linuskjk/CableProbe/zine/cool-bg.png

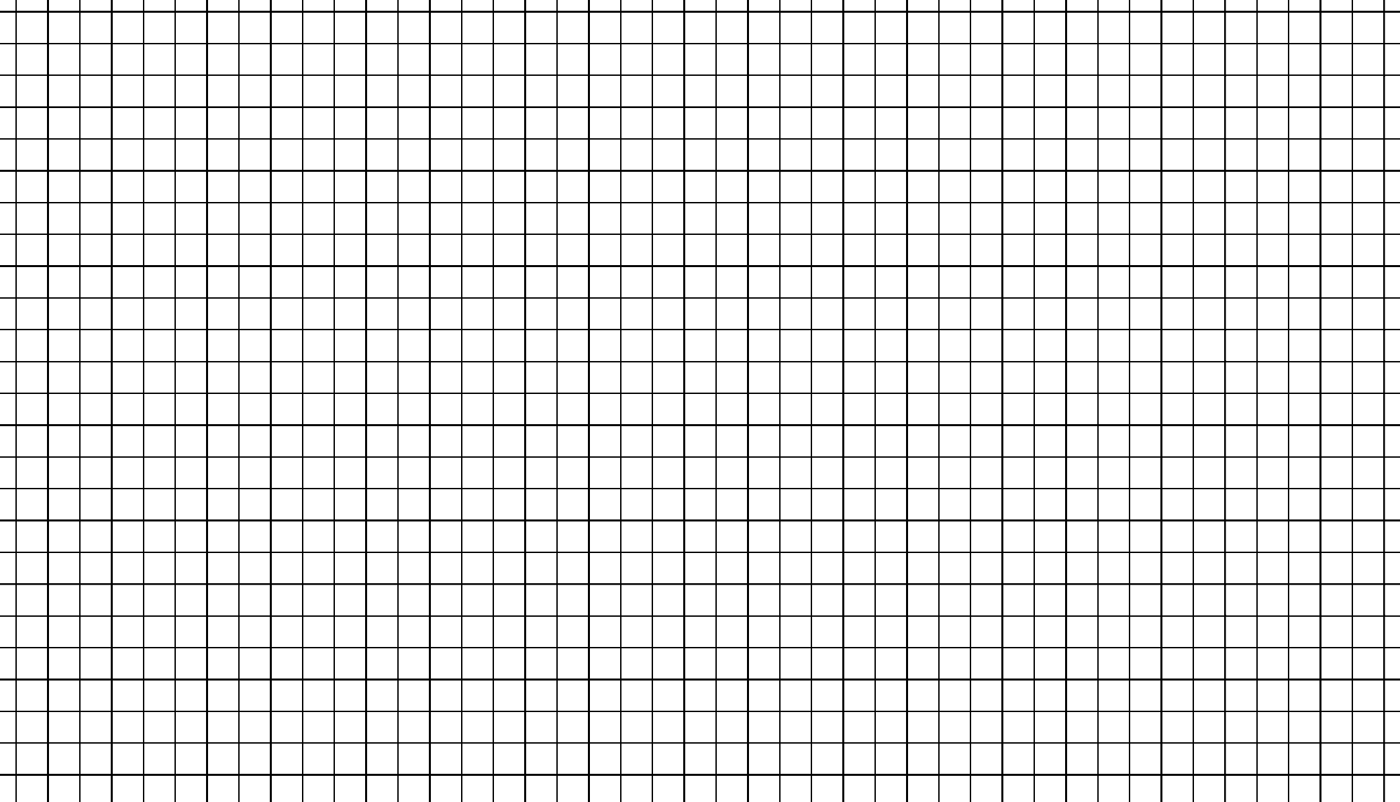
zine/cool-bg.png
