linuskjk/CableProbe/zine/main.png

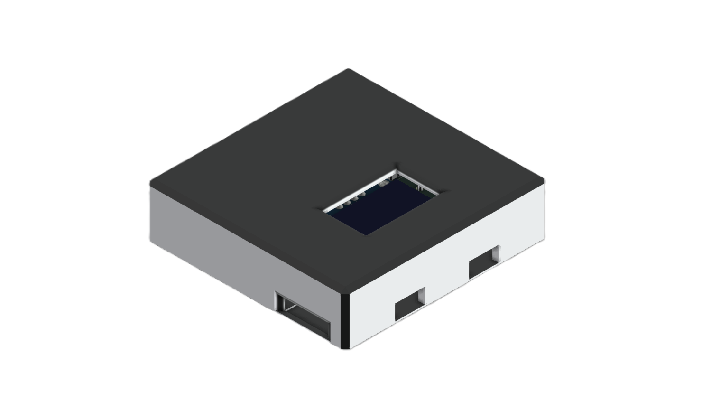
zine/main.png
