linuskjk/CableProbe/zine/oled.jpeg

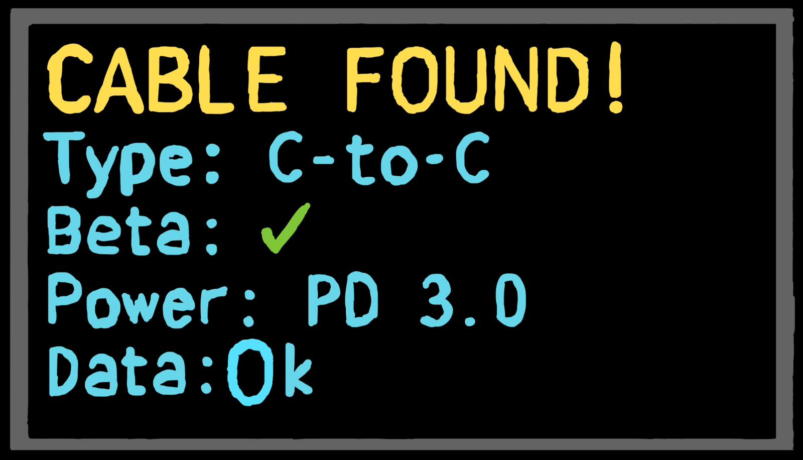
zine/oled.jpeg
