linuskjk/CableProbe/zine/sym.png

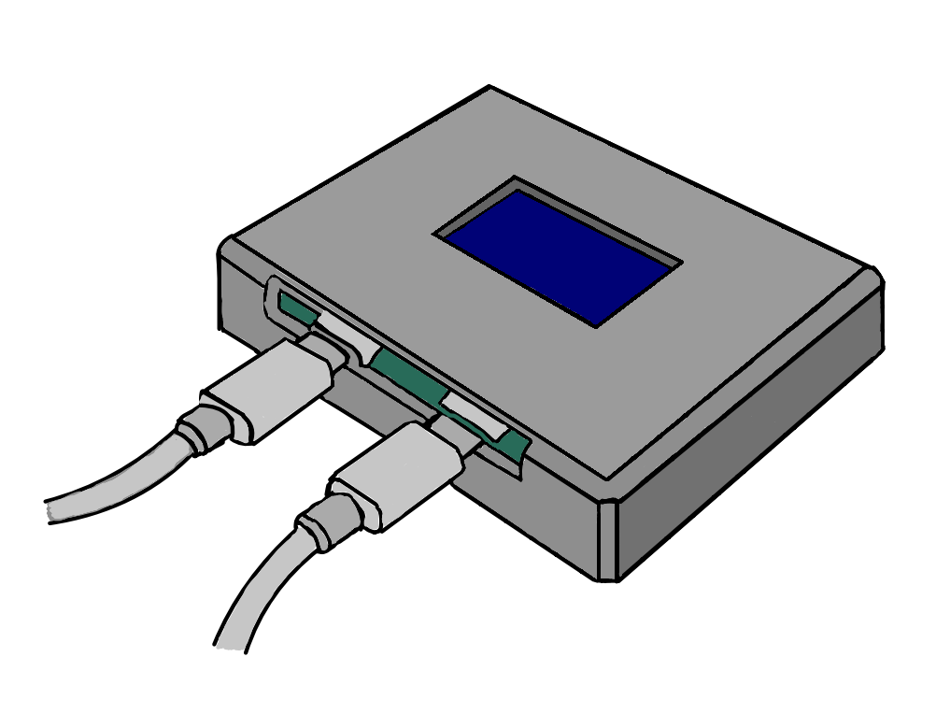
zine/sym.png
